ECEN2440finalProject/quade/gait.h

/*
 * gait.h
 *
 *  Created on: Nov 18, 2020
 *      Author: terry
 */

#ifndef GAIT_H_
#define GAIT_H_

#include "servo.h"
#include "parse_joystick.h"
#include "pca9685.h"


void servo_gait(int8_t * pos);

#endif /* GAIT_H_ */
