ECEN2440finalProject/quade/adc14.c

/* --COPYRIGHT--,BSD
 * Copyright (c) 2017, Texas Instruments Incorporated
 * All rights reserved.
 *
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
 * *  Redistributions of source code must retain the above copyright
 *    notice, this list of conditions and the following disclaimer.
 *
 * *  Redistributions in binary form must reproduce the above copyright
 *    notice, this list of conditions and the following disclaimer in the
 *    documentation and/or other materials provided with the distribution.
 *
 * *  Neither the name of Texas Instruments Incorporated nor the names of
 *    its contributors may be used to endorse or promote products derived
 *    from this software without specific prior written permission.
 *
 * THIS SOFTWARE IS PROVIDED BY THE COPYRIGHT HOLDERS AND CONTRIBUTORS "AS IS"
 * AND ANY EXPRESS OR IMPLIED WARRANTIES, INCLUDING, BUT NOT LIMITED TO,
 * THE IMPLIED WARRANTIES OF MERCHANTABILITY AND FITNESS FOR A PARTICULAR
 * PURPOSE ARE DISCLAIMED. IN NO EVENT SHALL THE COPYRIGHT OWNER OR
 * CONTRIBUTORS BE LIABLE FOR ANY DIRECT, INDIRECT, INCIDENTAL, SPECIAL,
 * EXEMPLARY, OR CONSEQUENTIAL DAMAGES (INCLUDING, BUT NOT LIMITED TO,
 * PROCUREMENT OF SUBSTITUTE GOODS OR SERVICES; LOSS OF USE, DATA, OR PROFITS;
 * OR BUSINESS INTERRUPTION) HOWEVER CAUSED AND ON ANY THEORY OF LIABILITY,
 * WHETHER IN CONTRACT, STRICT LIABILITY, OR TORT (INCLUDING NEGLIGENCE OR
 * OTHERWISE) ARISING IN ANY WAY OUT OF THE USE OF THIS SOFTWARE,
 * EVEN IF ADVISED OF THE POSSIBILITY OF SUCH DAMAGE.
 * --/COPYRIGHT--*/
/* Standard Includes */
#include <stdint.h>
#include <stdbool.h>

/* DriverLib Includes */
#include <adc14.h>
#include <debug.h>
#include <interrupt.h>

/* Statics */
static volatile uint32_t* const _ctlRegs[32] =
{ &ADC14->MCTL[0], &ADC14->MCTL[1], &ADC14->MCTL[2], &ADC14->MCTL[3],
        &ADC14->MCTL[4], &ADC14->MCTL[5], &ADC14->MCTL[6], &ADC14->MCTL[7],
        &ADC14->MCTL[8], &ADC14->MCTL[9], &ADC14->MCTL[10],
        &ADC14->MCTL[11], &ADC14->MCTL[12], &ADC14->MCTL[13],
        &ADC14->MCTL[14], &ADC14->MCTL[15], &ADC14->MCTL[16],
        &ADC14->MCTL[17], &ADC14->MCTL[18], &ADC14->MCTL[19],
        &ADC14->MCTL[20], &ADC14->MCTL[21], &ADC14->MCTL[22],
        &ADC14->MCTL[23], &ADC14->MCTL[24], &ADC14->MCTL[25],
        &ADC14->MCTL[26], &ADC14->MCTL[27], &ADC14->MCTL[28],
        &ADC14->MCTL[29], &ADC14->MCTL[30], &ADC14->MCTL[31] };

static uint_fast8_t _getIndexForMemRegister(uint32_t reg)
{
    switch (reg)
    {
    case ADC_MEM0:
        return 0;
    case ADC_MEM1:
        return 1;
    case ADC_MEM2:
        return 2;
    case ADC_MEM3:
        return 3;
    case ADC_MEM4:
        return 4;
    case ADC_MEM5:
        return 5;
    case ADC_MEM6:
        return 6;
    case ADC_MEM7:
        return 7;
    case ADC_MEM8:
        return 8;
    case ADC_MEM9:
        return 9;
    case ADC_MEM10:
        return 10;
    case ADC_MEM11:
        return 11;
    case ADC_MEM12:
        return 12;
    case ADC_MEM13:
        return 13;
    case ADC_MEM14:
        return 14;
    case ADC_MEM15:
        return 15;
    case ADC_MEM16:
        return 16;
    case ADC_MEM17:
        return 17;
    case ADC_MEM18:
        return 18;
    case ADC_MEM19:
        return 19;
    case ADC_MEM20:
        return 20;
    case ADC_MEM21:
        return 21;
    case ADC_MEM22:
        return 22;
    case ADC_MEM23:
        return 23;
    case ADC_MEM24:
        return 24;
    case ADC_MEM25:
        return 25;
    case ADC_MEM26:
        return 26;
    case ADC_MEM27:
        return 27;
    case ADC_MEM28:
        return 28;
    case ADC_MEM29:
        return 29;
    case ADC_MEM30:
        return 30;
    case ADC_MEM31:
        return 31;
    default:
        ASSERT(false);
        return ADC_INVALID_MEM;

    }
}

//*****************************************************************************
//
//!
//! Returns a boolean value that tells if conversion is active/running or is
//! not acMSP432 ted.
//!
//! Originally a public function, but moved to static. External customers should
//! use the ADC14_isBusy function.
//!
//! \return true if conversion is active, false otherwise
//
//*****************************************************************************
static bool ADCIsConversionRunning(void)
{
    return BITBAND_PERI(ADC14->CTL0, ADC14_CTL0_BUSY_OFS);
}

void ADC14_enableModule(void)
{
    BITBAND_PERI(ADC14->CTL0, ADC14_CTL0_ON_OFS) = 1;
}

bool ADC14_disableModule(void)
{
    if (ADCIsConversionRunning())
        return false;

    BITBAND_PERI(ADC14->CTL0, ADC14_CTL0_ON_OFS) = 0;

    return true;
}

bool ADC14_enableSampleTimer(uint32_t multiSampleConvert)
{
    if (ADCIsConversionRunning())
        return false;

    BITBAND_PERI(ADC14->CTL0, ADC14_CTL0_SHP_OFS) = 1;

    if (multiSampleConvert == ADC_MANUAL_ITERATION)
    {
        BITBAND_PERI(ADC14->CTL0, ADC14_CTL0_MSC_OFS) = 0;
    } else
    {
        BITBAND_PERI(ADC14->CTL0, ADC14_CTL0_MSC_OFS) = 1;
    }

    return true;
}

bool ADC14_disableSampleTimer(void)
{
    if (ADCIsConversionRunning())
        return false;

    BITBAND_PERI(ADC14->CTL0, ADC14_CTL0_SHP_OFS) = 0;

    return true;
}

bool ADC14_initModule(uint32_t clockSource, uint32_t clockPredivider,
        uint32_t clockDivider, uint32_t internalChannelMask)
{
    ASSERT(
            clockSource == ADC_CLOCKSOURCE_ADCOSC
            || clockSource == ADC_CLOCKSOURCE_SYSOSC
            || clockSource == ADC_CLOCKSOURCE_ACLK
            || clockSource == ADC_CLOCKSOURCE_MCLK
            || clockSource == ADC_CLOCKSOURCE_SMCLK
            || clockSource == ADC_CLOCKSOURCE_HSMCLK);

    ASSERT(
            clockPredivider == ADC_PREDIVIDER_1
            || clockPredivider == ADC_PREDIVIDER_4
            || clockPredivider == ADC_PREDIVIDER_32
            || clockPredivider == ADC_PREDIVIDER_64);

    ASSERT(
            clockDivider == ADC_DIVIDER_1 || clockDivider == ADC_DIVIDER_2
            || clockDivider == ADC_DIVIDER_3
            || clockDivider == ADC_DIVIDER_4
            || clockDivider == ADC_DIVIDER_5
            || clockDivider == ADC_DIVIDER_6
            || clockDivider == ADC_DIVIDER_7
            || clockDivider == ADC_DIVIDER_8);

    ASSERT(
            !(internalChannelMask
                    & ~(ADC_MAPINTCH3 | ADC_MAPINTCH2 | ADC_MAPINTCH1
                            | ADC_MAPINTCH0 | ADC_TEMPSENSEMAP | ADC_BATTMAP)));

    if (ADCIsConversionRunning())
        return false;

    ADC14->CTL0 = (ADC14->CTL0
            & ~(ADC14_CTL0_PDIV_MASK | ADC14_CTL0_DIV_MASK | ADC14_CTL0_SSEL_MASK))
            | clockDivider | clockPredivider | clockSource;

    ADC14->CTL1 = (ADC14->CTL1
            & ~(ADC_MAPINTCH3 | ADC_MAPINTCH2 | ADC_MAPINTCH1 | ADC_MAPINTCH0
                    | ADC_TEMPSENSEMAP | ADC_BATTMAP)) | internalChannelMask;

    return true;
}

void ADC14_setResolution(uint32_t resolution)
{
    ASSERT(
            resolution == ADC_8BIT || resolution == ADC_10BIT
            || resolution == ADC_12BIT || resolution == ADC_14BIT);

    ADC14->CTL1 = (ADC14->CTL1 & ~ADC14_CTL1_RES_MASK) |  resolution;
}

uint_fast32_t ADC14_getResolution(void)
{
    return ADC14->CTL1 & ADC14_CTL1_RES_MASK;
}

bool ADC14_setSampleHoldTrigger(uint32_t source, bool invertSignal)
{

    ASSERT(
            source == ADC_TRIGGER_ADCSC || source == ADC_TRIGGER_SOURCE1
            || source == ADC_TRIGGER_SOURCE2
            || source == ADC_TRIGGER_SOURCE3
            || source == ADC_TRIGGER_SOURCE4
            || source == ADC_TRIGGER_SOURCE5
            || source == ADC_TRIGGER_SOURCE6
            || source == ADC_TRIGGER_SOURCE7);

    if (ADCIsConversionRunning())
        return false;

    if (invertSignal)
    {
        ADC14->CTL0 = (ADC14->CTL0
                & ~(ADC14_CTL0_ISSH | ADC14_CTL0_SHS_MASK)) | source
                | ADC14_CTL0_ISSH;
    } else
    {
        ADC14->CTL0 = (ADC14->CTL0
                & ~(ADC14_CTL0_ISSH | ADC14_CTL0_SHS_MASK)) | source;
    }

    return true;
}

bool ADC14_setSampleHoldTime(uint32_t firstPulseWidth,
        uint32_t secondPulseWidth)
{
    ASSERT(
            firstPulseWidth == ADC_PULSE_WIDTH_4
            || firstPulseWidth == ADC_PULSE_WIDTH_8
            || firstPulseWidth == ADC_PULSE_WIDTH_16
            || firstPulseWidth == ADC_PULSE_WIDTH_32
            || firstPulseWidth == ADC_PULSE_WIDTH_64
            || firstPulseWidth == ADC_PULSE_WIDTH_96
            || firstPulseWidth == ADC_PULSE_WIDTH_128
            || firstPulseWidth == ADC_PULSE_WIDTH_192);

    ASSERT(
            secondPulseWidth == ADC_PULSE_WIDTH_4
            || secondPulseWidth == ADC_PULSE_WIDTH_8
            || secondPulseWidth == ADC_PULSE_WIDTH_16
            || secondPulseWidth == ADC_PULSE_WIDTH_32
            || secondPulseWidth == ADC_PULSE_WIDTH_64
            || secondPulseWidth == ADC_PULSE_WIDTH_96
            || secondPulseWidth == ADC_PULSE_WIDTH_128
            || secondPulseWidth == ADC_PULSE_WIDTH_192);

    if (ADCIsConversionRunning())
        return false;

    ADC14->CTL0 = (ADC14->CTL0
            & ~(ADC14_CTL0_SHT0_MASK | ADC14_CTL0_SHT1_MASK)) | secondPulseWidth
            | (firstPulseWidth >> 4);

    return true;
}

bool ADC14_configureMultiSequenceMode(uint32_t memoryStart, uint32_t memoryEnd,
bool repeatMode)
{
    uint32_t ii;

    ASSERT(
            _getIndexForMemRegister(memoryStart) != ADC_INVALID_MEM
            && _getIndexForMemRegister(memoryEnd) != ADC_INVALID_MEM);

    if (ADCIsConversionRunning())
        return false;

    /* Clearing out any lingering EOS */
    for (ii = 0; ii < 32; ii++)
    {
        BITBAND_PERI(*(_ctlRegs[ii]), ADC14_MCTLN_EOS_OFS) = 0;
    }

    uint_fast8_t memEndIndex = _getIndexForMemRegister(memoryEnd);
    if (memEndIndex != ADC_INVALID_MEM)
    {
        /* Setting Start/Stop locations */
        BITBAND_PERI(
                (*(_ctlRegs[memEndIndex])),
                ADC14_MCTLN_EOS_OFS) = 1;

        ADC14->CTL1 = (ADC14->CTL1 & ~(ADC14_CTL1_CSTARTADD_MASK))
                        | (_getIndexForMemRegister(memoryStart) << 16);

        /* Setting multiple sample mode */
        if (!repeatMode)
        {
            ADC14->CTL0 = (ADC14->CTL0 & ~(ADC14_CTL0_CONSEQ_MASK))
                    | (ADC14_CTL0_CONSEQ_1);
        } else
        {
            ADC14->CTL0 = (ADC14->CTL0 & ~(ADC14_CTL0_CONSEQ_MASK))
                    | (ADC14_CTL0_CONSEQ_3);
        }

        return true;
    }
    else
    {
        return false;
    }
}

bool ADC14_configureSingleSampleMode(uint32_t memoryDestination,
bool repeatMode)
{
    ASSERT(_getIndexForMemRegister(memoryDestination) != 32);

    if (ADCIsConversionRunning())
        return false;

    /* Setting the destination register */
    ADC14->CTL1 = (ADC14->CTL1 & ~(ADC14_CTL1_CSTARTADD_MASK))
            | (_getIndexForMemRegister(memoryDestination) << 16);

    /* Setting single sample mode */
    if (!repeatMode)
    {
        ADC14->CTL0 = (ADC14->CTL0 & ~(ADC14_CTL0_CONSEQ_MASK))
                | (ADC14_CTL0_CONSEQ_0);
    } else
    {
        ADC14->CTL0 = (ADC14->CTL0 & ~(ADC14_CTL0_CONSEQ_MASK))
                | (ADC14_CTL0_CONSEQ_2);
    }

    return true;
}

bool ADC14_enableConversion(void)
{
    if (ADCIsConversionRunning() || !BITBAND_PERI(ADC14->CTL0, ADC14_CTL0_ON_OFS))
        return false;

    ADC14->CTL0 |= (ADC14_CTL0_ENC);

    return true;
}

bool ADC14_toggleConversionTrigger(void)
{
    if (!BITBAND_PERI(ADC14->CTL0, ADC14_CTL0_ON_OFS))
        return false;

    if (BITBAND_PERI(ADC14->CTL0, ADC14_CTL0_SC_OFS))
    {
        BITBAND_PERI(ADC14->CTL0, ADC14_CTL0_SC_OFS) = 0;
    } else
    {
        BITBAND_PERI(ADC14->CTL0, ADC14_CTL0_SC_OFS) = 1;
    }

    return true;
}

void ADC14_disableConversion(void)
{
    ADC14->CTL0 &= ~(ADC14_CTL0_SC | ADC14_CTL0_ENC);
}

bool ADC14_isBusy(void)
{
    return BITBAND_PERI(ADC14->CTL0, ADC14_CTL0_BUSY_OFS);
}

bool ADC14_configureConversionMemory(uint32_t memorySelect, uint32_t refSelect,
        uint32_t channelSelect, bool differntialMode)
{
    uint32_t currentReg, ii;
    uint32_t *curReg;

    /* Initialization */
    ii = 1;
    currentReg = 0x01;

    if (ADCIsConversionRunning())
        return false;

    while (memorySelect != 0)
    {
        if (!(memorySelect & ii))
        {
            ii = ii << 1;
            continue;
        }

        currentReg = memorySelect & ii;
        memorySelect &= ~ii;
        ii = ii << 1;

        uint_fast8_t currRegIndex = _getIndexForMemRegister(currentReg);
        if (currRegIndex != ADC_INVALID_MEM)
        {
            curReg = (uint32_t*) _ctlRegs[currRegIndex];

            if (differntialMode)
            {
                (*curReg) = ((*curReg)
                        & ~(ADC14_MCTLN_VRSEL_MASK | ADC14_MCTLN_INCH_MASK
                                | ADC14_MCTLN_DIF))
                        | (channelSelect | refSelect | ADC14_MCTLN_DIF);
            } else
            {
                (*curReg) = ((*curReg)
                        & ~(ADC14_MCTLN_VRSEL_MASK | ADC14_MCTLN_INCH_MASK
                                | ADC14_MCTLN_DIF)) | (channelSelect | refSelect);
            }
        }
        else
        {
            return false;
        }
    }

    return true;
}

bool ADC14_enableComparatorWindow(uint32_t memorySelect, uint32_t windowSelect)
{
    uint32_t currentReg, ii;
    uint32_t *curRegPoint;

    /* Initialization */
    ii = 1;
    currentReg = 0x01;

    if (ADCIsConversionRunning())
        return false;

    while (memorySelect != 0)
    {
        if (!(memorySelect & ii))
        {
            ii = ii << 1;
            continue;
        }

        currentReg = memorySelect & ii;
        memorySelect &= ~ii;
        ii = ii << 1;

        uint_fast8_t currRegIndex = _getIndexForMemRegister(currentReg);
        if (currRegIndex != ADC_INVALID_MEM)
        {
            curRegPoint =
                    (uint32_t*) _ctlRegs[currRegIndex];

            if (windowSelect == ADC_COMP_WINDOW0)
            {
                (*curRegPoint) = ((*curRegPoint)
                        & ~(ADC14_MCTLN_WINC | ADC14_MCTLN_WINCTH))
                        | (ADC14_MCTLN_WINC);
            } else if (windowSelect == ADC_COMP_WINDOW1)
            {
                (*curRegPoint) |= ADC14_MCTLN_WINC | ADC14_MCTLN_WINCTH;
            }
        }
        else
        {
            return false;
        }

    }

    return true;
}

bool ADC14_disableComparatorWindow(uint32_t memorySelect)
{
    uint32_t currentReg, ii;

    /* Initialization */
    ii = 1;
    currentReg = 0x01;

    if (ADCIsConversionRunning())
        return false;

    while (memorySelect != 0)
    {
        if (!(memorySelect & ii))
        {
            ii = ii << 1;
            continue;
        }

        currentReg = memorySelect & ii;
        memorySelect &= ~ii;
        ii = ii << 1;

        (*(_ctlRegs[_getIndexForMemRegister(currentReg)])) &=
                ~ADC14_MCTLN_WINC;

    }

    return true;
}

bool ADC14_setComparatorWindowValue(uint32_t window, int16_t low, int16_t high)
{
    if (ADCIsConversionRunning())
        return false;

    if(BITBAND_PERI(ADC14->CTL1, ADC14_CTL1_DF_OFS))
    {
        low = ((low << 2) | (0x8000 & low)) & 0xFFFC;
        high = ((high << 2) | (0x8000 & high)) & 0xFFFC;
    }

    if (window == ADC_COMP_WINDOW0)
    {
        ADC14->HI0 = (high);
        ADC14->LO0 = (low);

    } else if (window == ADC_COMP_WINDOW1)
    {
        ADC14->HI1 = (high);
        ADC14->LO1 = (low);

    } else
    {
        ASSERT(false);
        return false;
    }

    return true;
}

bool ADC14_setResultFormat(uint32_t resultFormat)
{
    if (ADCIsConversionRunning())
        return false;

    if (resultFormat == ADC_UNSIGNED_BINARY)
    {
        BITBAND_PERI(ADC14->CTL1, ADC14_CTL1_DF_OFS) = 0;
    } else if (resultFormat == ADC_SIGNED_BINARY)
    {
        BITBAND_PERI(ADC14->CTL1, ADC14_CTL1_DF_OFS) = 1;
    } else
    {
        ASSERT(false);
    }

    return true;
}

uint_fast16_t ADC14_getResult(uint32_t memorySelect)
{
    uint_fast8_t memSelIndex = _getIndexForMemRegister(memorySelect);
    if (memSelIndex != ADC_INVALID_MEM)
    {
        return *((uint16_t*) (_ctlRegs[memSelIndex]
                + 0x20));
    }
    else
    {
        return 0;
    }
}

void ADC14_getMultiSequenceResult(uint16_t* res)
{

    uint32_t startIndex, ii;

    startIndex = (ADC14->CTL1 & ADC14_CTL1_CSTARTADD_MASK)>>16;

    for (ii = startIndex; ii < 32; ii++)
    {
        res[ii] = ADC14->MEM[ii];

        if(ADC14->MCTL[ii] & ADC14_MCTLN_EOS)
            break;

    }

}

void ADC14_getResultArray(uint32_t memoryStart, uint32_t memoryEnd,
        uint16_t* res)
{
    uint32_t ii = 0;
    uint32_t *firstPoint, *secondPoint;

    bool foundEnd = false;

    uint_fast8_t memStartIndex, memEndIndex;

    memStartIndex = _getIndexForMemRegister(memoryStart);
    memEndIndex = _getIndexForMemRegister(memoryEnd);

    ASSERT(
            _getIndexForMemRegister(memoryStart) != ADC_INVALID_MEM
            && _getIndexForMemRegister(memoryEnd) != ADC_INVALID_MEM);

    if (memStartIndex != ADC_INVALID_MEM && memEndIndex!= ADC_INVALID_MEM) {
        firstPoint = (uint32_t*) _ctlRegs[memStartIndex];
        secondPoint = (uint32_t*) _ctlRegs[memEndIndex];

        while (!foundEnd)
        {
            if (firstPoint == secondPoint)
            {
                foundEnd = true;
            }

            res[ii] = *(((uint16_t*) firstPoint) + 0x40);

            if (firstPoint == _ctlRegs[31])
                firstPoint = (uint32_t*) _ctlRegs[0];
            else
                firstPoint += 0x04;
        }
    }
}

bool ADC14_enableReferenceBurst(void)
{
    if (ADCIsConversionRunning())
        return false;

    BITBAND_PERI(ADC14->CTL1, ADC14_CTL1_REFBURST_OFS) = 1;

    return true;
}

bool ADC14_disableReferenceBurst(void)
{
    if (ADCIsConversionRunning())
        return false;

    BITBAND_PERI(ADC14->CTL1, ADC14_CTL1_REFBURST_OFS) = 0;

    return true;
}

bool ADC14_setPowerMode(uint32_t adcPowerMode)
{
    if (ADCIsConversionRunning())
        return false;

    switch (adcPowerMode)
    {
    case ADC_UNRESTRICTED_POWER_MODE:
        ADC14->CTL1 = (ADC14->CTL1 & ~(ADC14_CTL1_PWRMD_MASK))
                | (ADC14_CTL1_PWRMD_0);
        break;
    case ADC_ULTRA_LOW_POWER_MODE:
        ADC14->CTL1 = (ADC14->CTL1 & ~(ADC14_CTL1_PWRMD_MASK))
                | (ADC14_CTL1_PWRMD_2);
        break;
    default:
        ASSERT(false);
        return false;
    }

    return true;
}

void ADC14_enableInterrupt(uint_fast64_t mask)
{
    uint32_t stat = mask & 0xFFFFFFFF;

    ADC14->IER0 |= stat;
    stat = (mask >> 32);
    ADC14->IER1 |= (stat);
}

void ADC14_disableInterrupt(uint_fast64_t mask)
{
    uint32_t stat = mask & 0xFFFFFFFF;

    ADC14->IER0 &= ~stat;
    stat = (mask >> 32);
    ADC14->IER1 &= ~(stat);
}

uint_fast64_t ADC14_getInterruptStatus(void)
{
    uint_fast64_t status = ADC14->IFGR1;
    return ((status << 32) | ADC14->IFGR0);
}

uint_fast64_t ADC14_getEnabledInterruptStatus(void)
{
    uint_fast64_t stat = ADC14->IER1;

    return ADC14_getInterruptStatus() & ((stat << 32) | ADC14->IER0);

}

void ADC14_clearInterruptFlag(uint_fast64_t mask)
{
    uint32_t stat = mask & 0xFFFFFFFF;

    ADC14->CLRIFGR0 |= stat;
    stat = (mask >> 32);
    ADC14->CLRIFGR1 |= (stat);
}

void ADC14_registerInterrupt(void (*intHandler)(void))
{
    //
    // Register the interrupt handler, returning an error if an error occurs.
    //
    Interrupt_registerInterrupt(INT_ADC14, intHandler);

    //
    // Enable the ADC interrupt.
    //
    Interrupt_enableInterrupt(INT_ADC14);
}

void ADC14_unregisterInterrupt(void)
{
    //
    // Disable the interrupt.
    //
    Interrupt_disableInterrupt(INT_ADC14);

    //
    // Unregister the interrupt handler.
    //
    Interrupt_unregisterInterrupt(INT_ADC14);
}
